PatrickDuong3001/Mobile_Tick_Trap/Drive Shaft - Part 1.stl

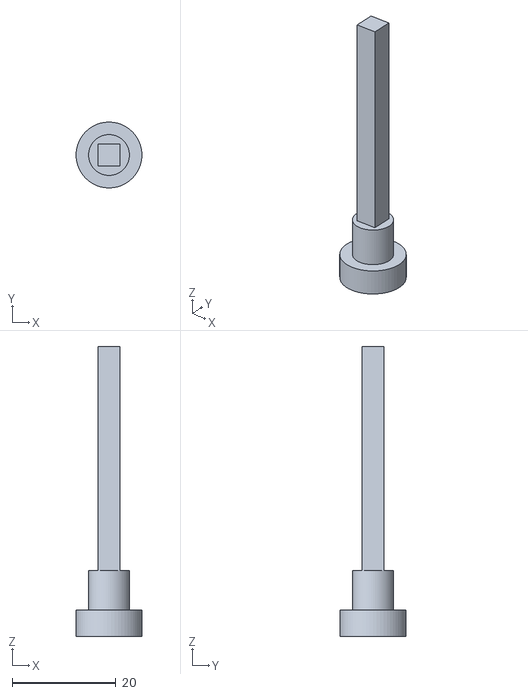
[picture p23: CAD file, 2022-02-15]
Drive Shaft - Part 1.stl
12.7 x 12.7 x 55.9
