PatrickDuong3001/Mobile_Tick_Trap/Wheel Concept - Part 1.stl

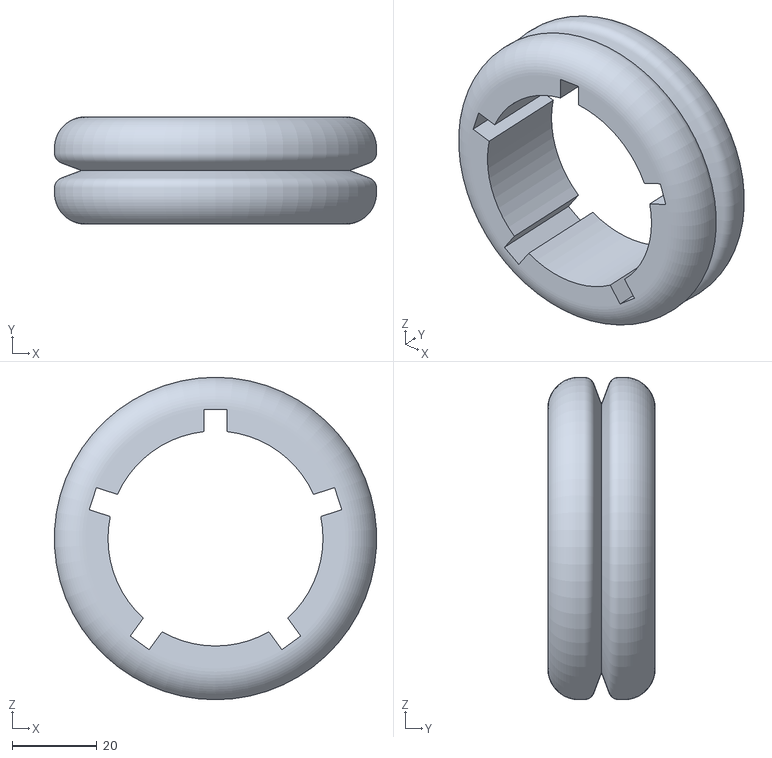
[picture p24: CAD file, 2022-02-15]
Wheel Concept - Part 1.stl
76.1 x 25.4 x 76.2
