PatrickDuong3001/Mobile_Tick_Trap/Drive Shaft - Part 3.stl

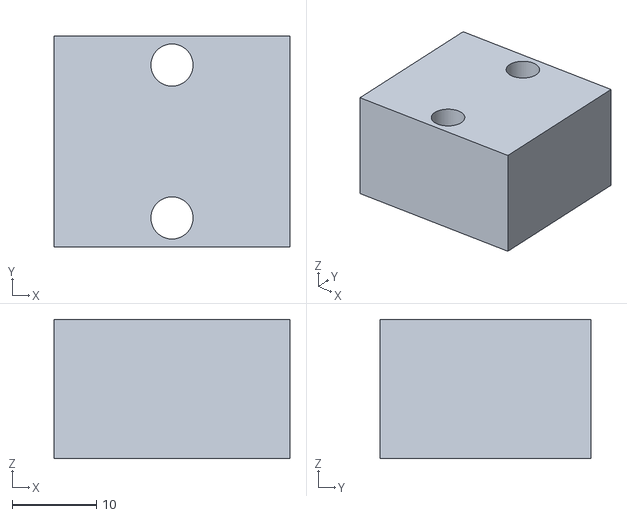
[picture p25: CAD file, 2022-02-15]
Drive Shaft - Part 3.stl
28.0 x 25.0 x 16.5
